jpasqua/FauxNeXT/images/Actual/Starting.jpeg

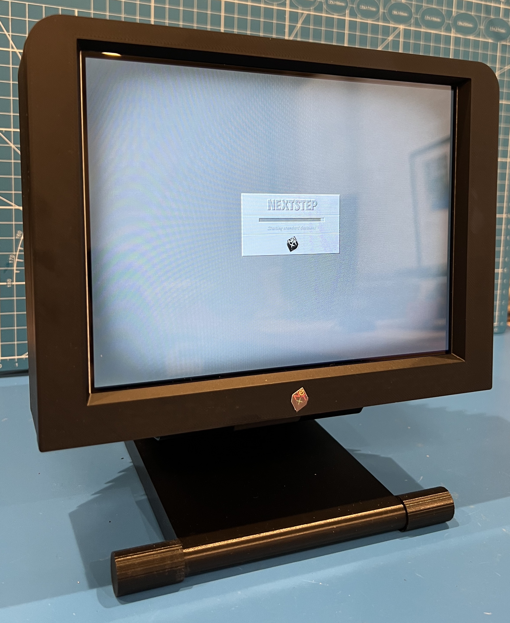
images/Actual/Starting.jpeg
