jpasqua/FauxNeXT/images/Model/FinAreaSupports.jpeg

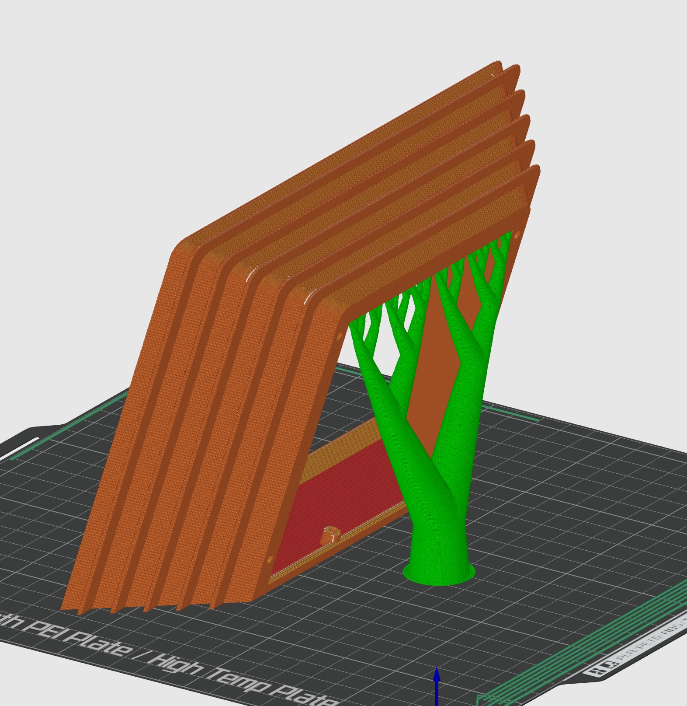
images/Model/FinAreaSupports.jpeg
