jpasqua/FauxNeXT/images/Model/LegSupports.jpeg

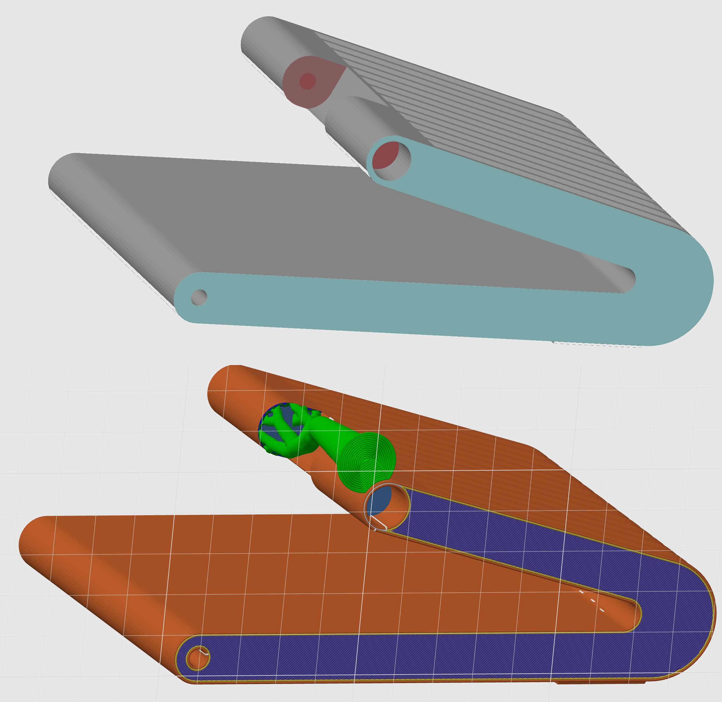
images/Model/LegSupports.jpeg
