jpasqua/FauxNeXT/images/SoundBox/CaseSupports.jpeg

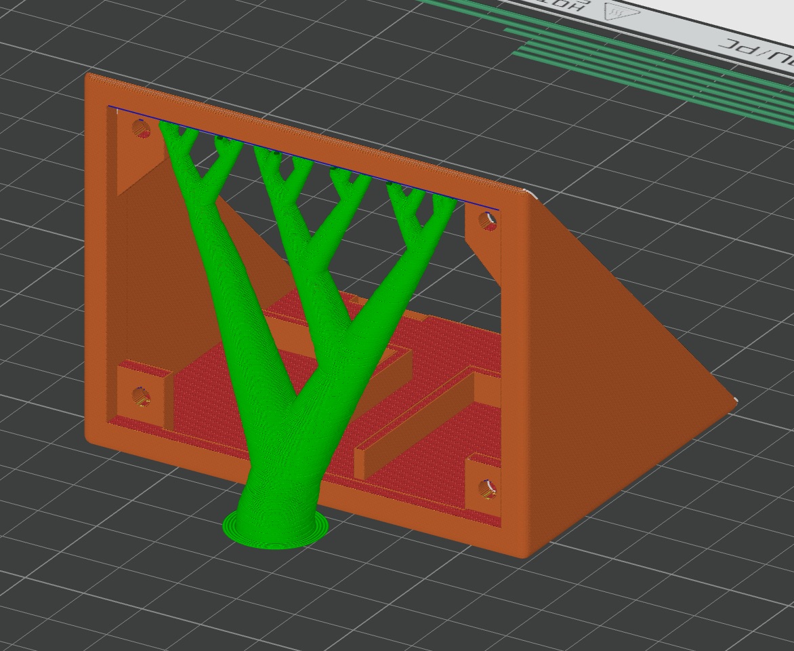
images/SoundBox/CaseSupports.jpeg
