jpasqua/FauxNeXT/images/SoundBox/Lid.jpeg

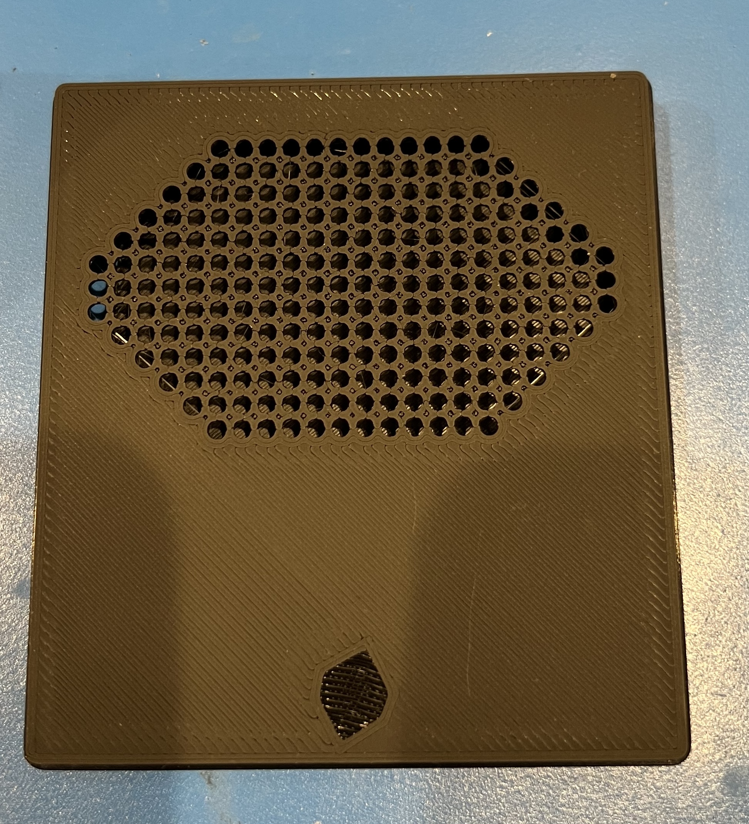
images/SoundBox/Lid.jpeg
