jpasqua/FauxNeXT/images/SoundBox/SpeakerTabs.jpeg

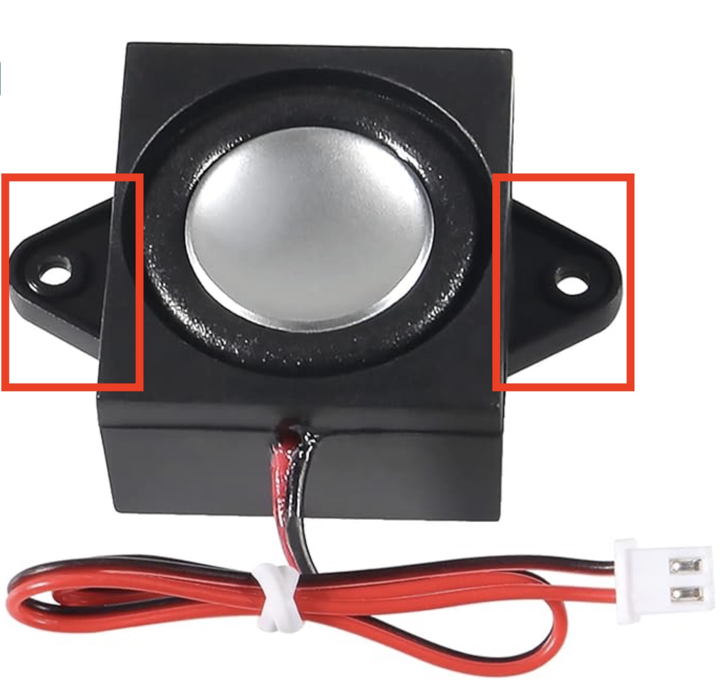
images/SoundBox/SpeakerTabs.jpeg
