jpasqua/FauxNeXT/images/SoundBox/USBSpeakerBoxBack.jpeg

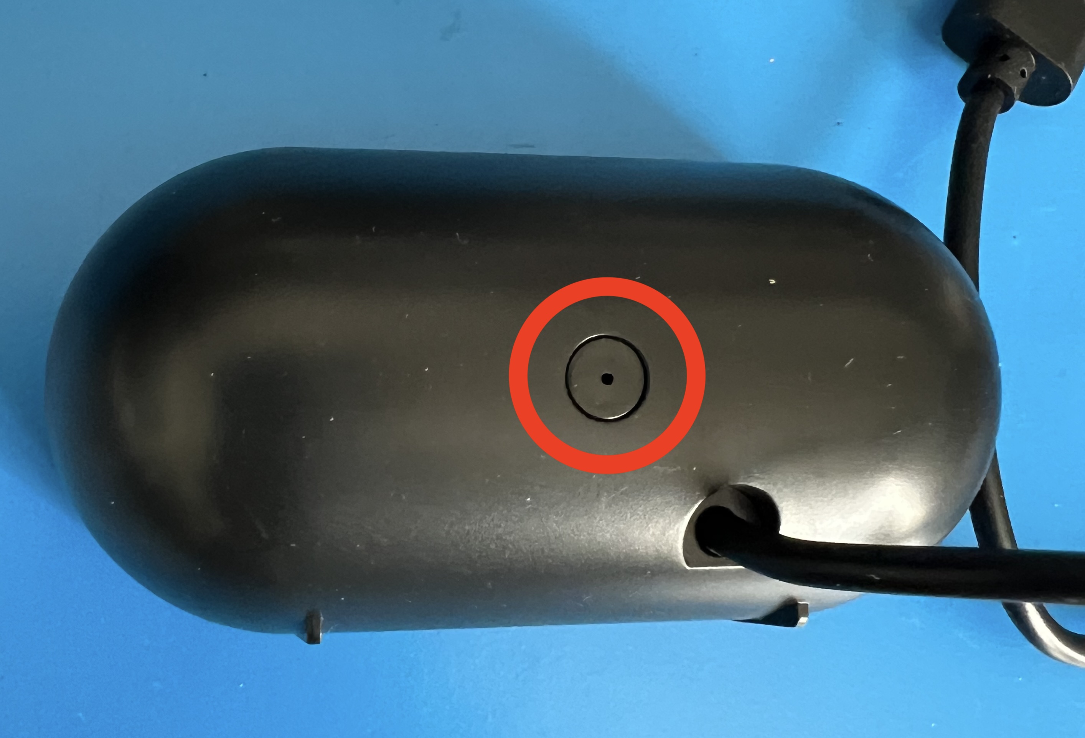
images/SoundBox/USBSpeakerBoxBack.jpeg
