jpasqua/FauxNeXT/images/SW/Boot.jpeg

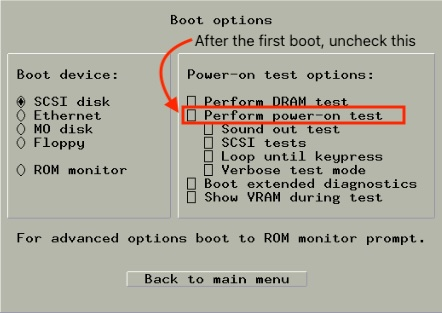
images/SW/Boot.jpeg
