jpasqua/FauxNeXT/images/SW/Floppy.png

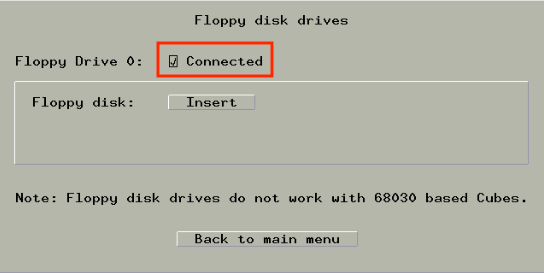
images/SW/Floppy.png
