jpasqua/FauxNeXT/images/SW/Graphics.png

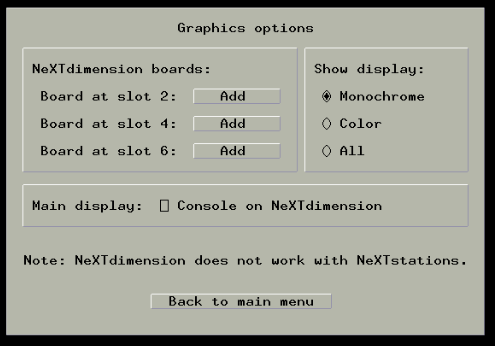
images/SW/Graphics.png
