jpasqua/FauxNeXT/images/SW/Keyboard.png

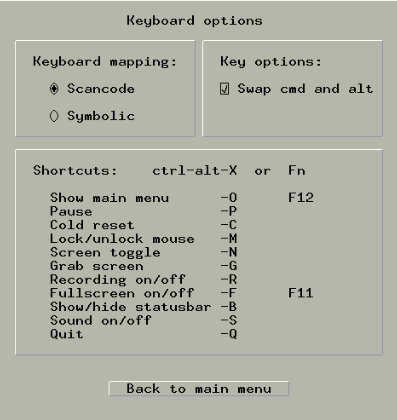
images/SW/Keyboard.png
