jpasqua/FauxNeXT/images/SW/MO.png

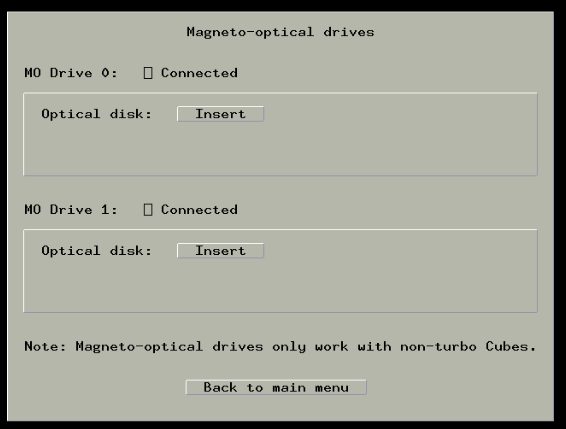
images/SW/MO.png
