jpasqua/FauxNeXT/images/SW/Mouse.png

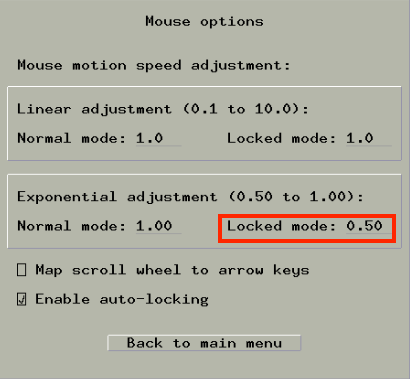
images/SW/Mouse.png
