jpasqua/FauxNeXT/images/SW/Network.png

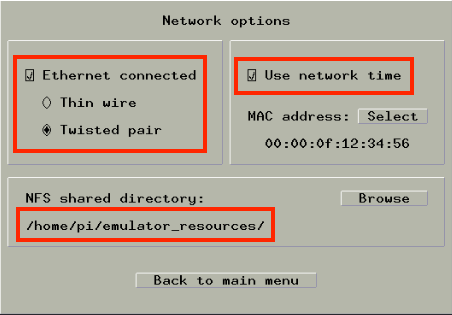
images/SW/Network.png
