jpasqua/FauxNeXT/images/SW/ROM.png

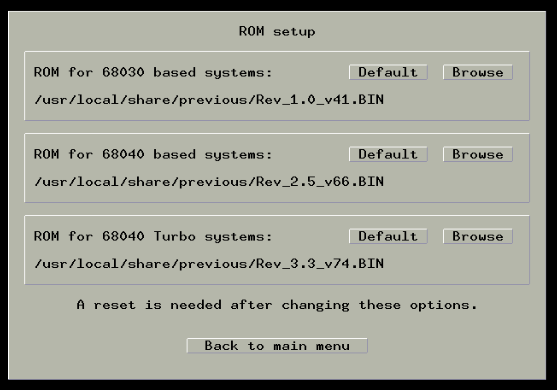
images/SW/ROM.png
