jpasqua/FauxNeXT/images/SW/SCSI.jpeg

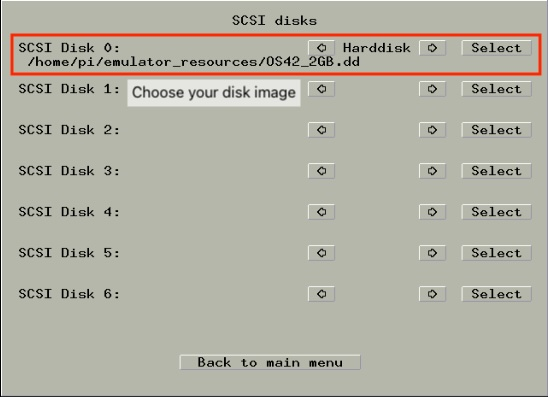
images/SW/SCSI.jpeg
