jpasqua/FauxNeXT/images/SW/Sound.png

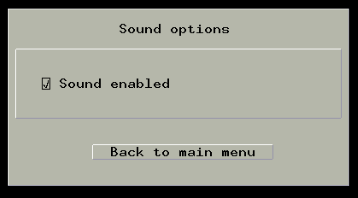
images/SW/Sound.png
