jpasqua/FauxNeXT/images/SW/System.jpeg

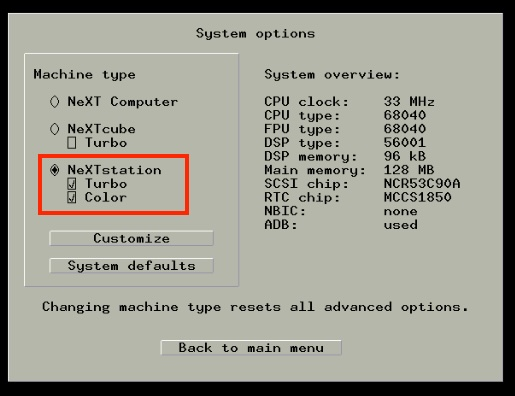
images/SW/System.jpeg
