jpasqua/FauxNeXT/images/SoundBox/AllParts.jpeg

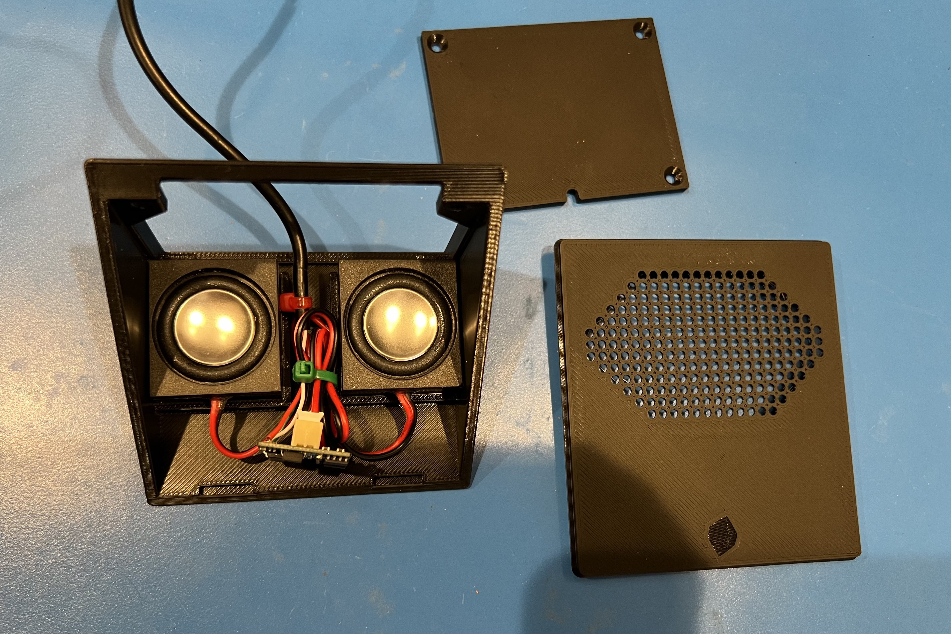
images/SoundBox/AllParts.jpeg
