jpasqua/FauxNeXT/STLs/Rear_Shell.3mf

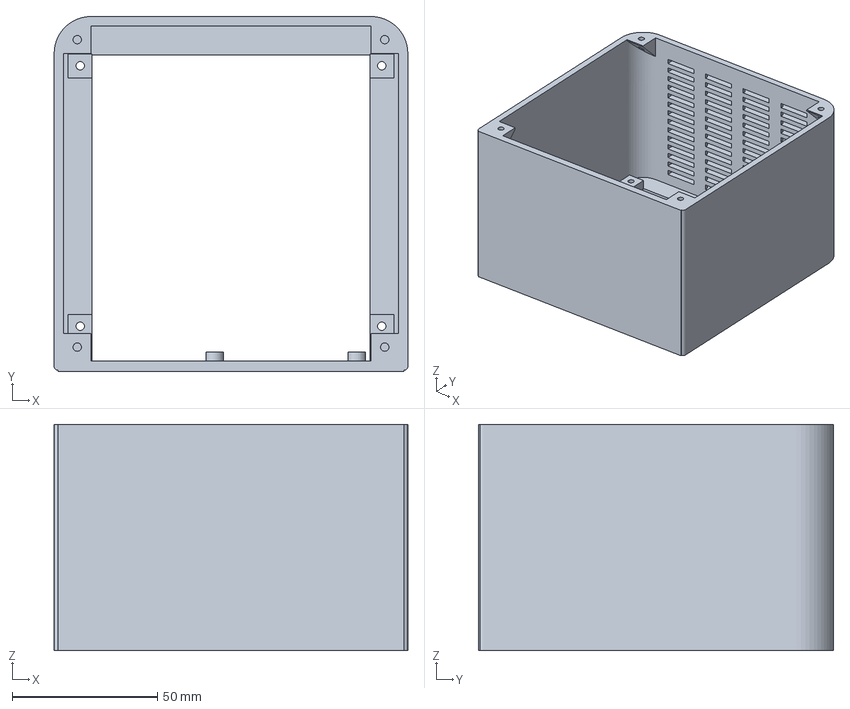
[picture p37: CAD file, 2024-08-16]
STLs/Rear_Shell.3mf
121.9 x 122.4 x 78.0 mm
