jpasqua/FauxNeXT/STLs/Rolling_Feet.3mf

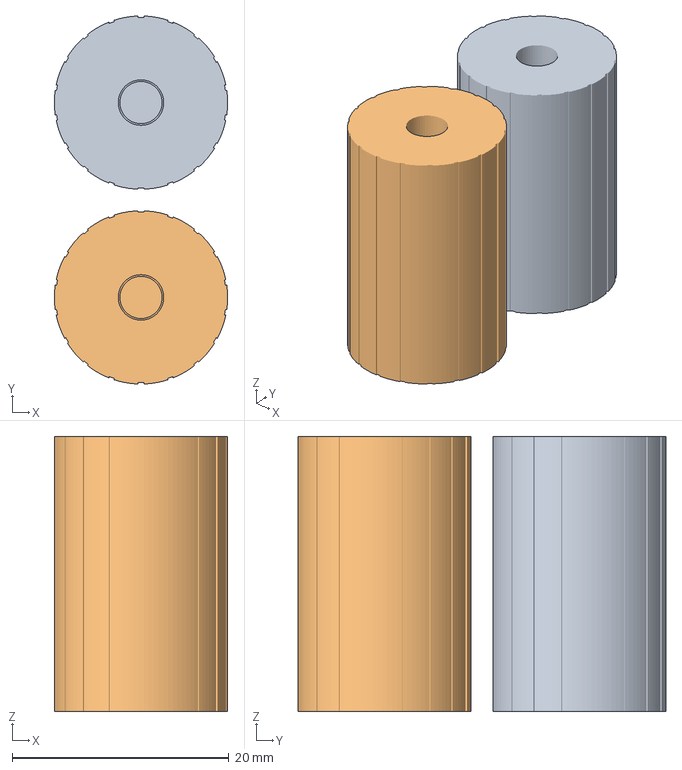
[picture p38: CAD file, 2024-08-16]
STLs/Rolling_Feet.3mf
16.0 x 34.0 x 25.4 mm
Rolling_Foot.stl x 2
