jpasqua/FauxNeXT/images/Assembly/SlideOnFins.gif

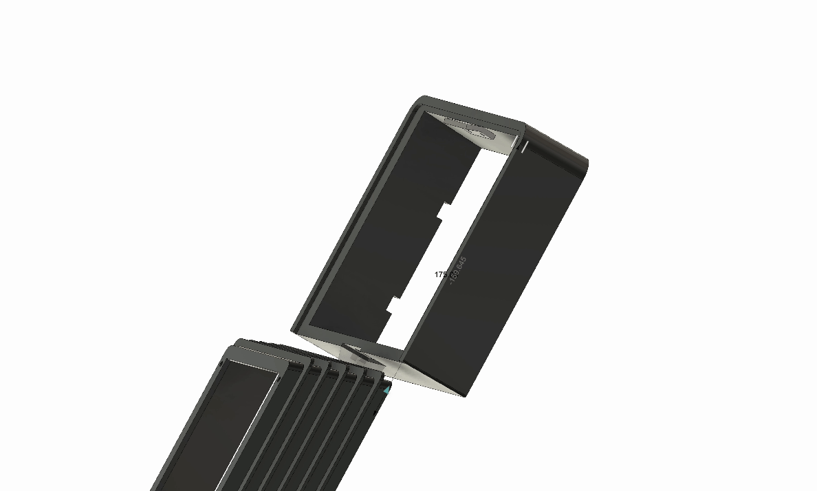
images/Assembly/SlideOnFins.gif
