jpasqua/FauxNeXT/images/Wiring/GPIOConnections.jpeg

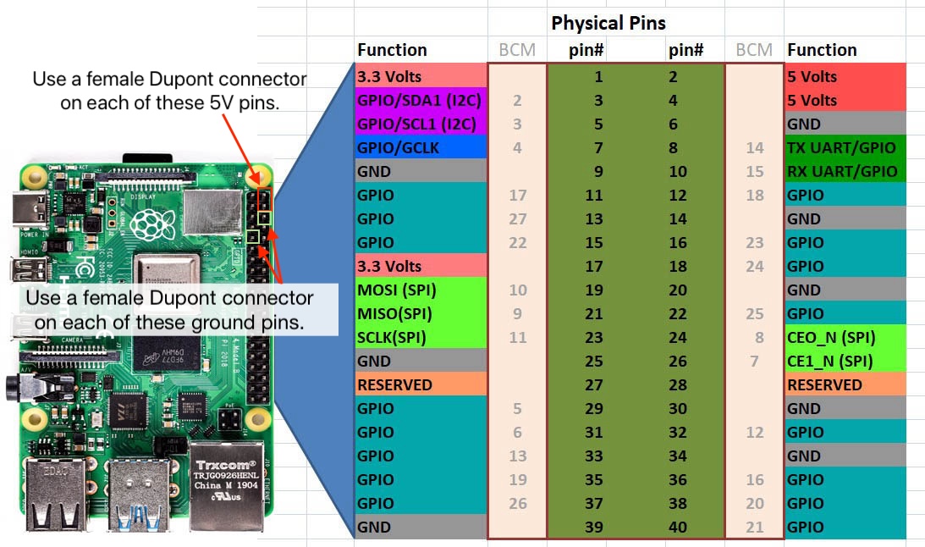
images/Wiring/GPIOConnections.jpeg
